lukasprojects/esp32-dalitester/DALI-Tester-ESP32-ILI9341/include/ui/dali_icons_38x38.h

#pragma once
#include <stdint.h>

// 1-bit monochrome icons, 38x38 pixels
// Row-packed, MSB first, 5 bytes per row (last 2 bits padding)

static const uint8_t DALI_ICON_WIDTH = 38;
static const uint8_t DALI_ICON_HEIGHT = 38;
static const uint8_t DALI_ICON_BYTES_PER_ROW = 5;

static const uint8_t icon_01_scan_devices[190] = {
    0x00, 0x00, 0x00, 0x00, 0x00, 0x00, 0x01, 0xFF, 0x80, 0x00,
    0x00, 0x0F, 0xFF, 0xE0, 0x00, 0x00, 0x3F, 0xFF, 0xF8, 0x00,
    0x00, 0x7F, 0x01, 0xFC, 0x00, 0x00, 0xF0, 0x00, 0x0F, 0x00,
    0x01, 0xE0, 0x00, 0x0F, 0x00, 0x03, 0xC0, 0x7C, 0x03, 0x80,
    0x07, 0x03, 0xFF, 0x01, 0xC0, 0x07, 0x03, 0xFF, 0xC1, 0xC0,
    0x0F, 0x03, 0xC7, 0xC1, 0xE0, 0x0E, 0x07, 0x81, 0xE0, 0xE0,
    0x0E, 0x0E, 0x00, 0xE0, 0xE0, 0x1C, 0x0E, 0x00, 0xE0, 0x60,
    0x1C, 0x0E, 0x00, 0xE0, 0x60, 0x1C, 0x0E, 0x00, 0x60, 0x60,
    0x1C, 0x0F, 0x00, 0xE0, 0x60, 0x1C, 0x07, 0x01, 0xE0, 0x60,
    0x1C, 0x07, 0x81, 0xC0, 0x60, 0x1C, 0x03, 0xC7, 0xC0, 0x60,
    0x1C, 0x01, 0xC7, 0x80, 0x60, 0x1E, 0x01, 0xC7, 0x00, 0xE0,
    0x0E, 0x01, 0xFF, 0x00, 0xE0, 0x0E, 0x00, 0x78, 0x00, 0xE0,
    0x0F, 0x00, 0xFE, 0x00, 0xE0, 0x07, 0x80, 0xFE, 0x03, 0xC0,
    0x03, 0xC0, 0xFE, 0x07, 0x80, 0x01, 0xE0, 0x7C, 0x07, 0x80,
    0x00, 0xE0, 0x00, 0x0F, 0x80, 0x00, 0x78, 0x00, 0x3F, 0xE0,
    0x00, 0x3F, 0x01, 0xFF, 0xE0, 0x00, 0x1F, 0xFF, 0xF7, 0xE0,
    0x00, 0x0F, 0xFF, 0xE3, 0xE0, 0x00, 0x01, 0xFF, 0x01, 0xE0,
    0x00, 0x00, 0x00, 0x00, 0xE0, 0x00, 0x00, 0x00, 0x00, 0x60,
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
    {"send_cmd", icon_07_send_cmd},
    {"broadcast_control", icon_08_broadcast_control},
    {"locate", icon_09_locate},
    {"bus_monitor", icon_10_bus_monitor},
    {"sd_card", icon_11_sd_card},
    {"wago_project", icon_12_wago_project},
    {"sd_busy", icon_13_sd_busy},
};
